MelanieT/PiLomar-pico-controller/tusb_lwip_glue.c

/* 
 * The MIT License (MIT)
 *
 * Based on tinyUSB example that is: Copyright (c) 2020 Peter Lawrence
 * Modified for Pico by Floris Bos
 *
 * influenced by lrndis https://github.com/fetisov/lrndis
 *
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
 */

#include "tusb_lwip_glue.h"

// HIPPY FIX
#include "pico/sync.h"

/* lwip context */
static struct netif netif_data;

/* shared between tud_network_recv_cb() and service_traffic() */
static struct pbuf *received_frame;

/* this is used by this code, ./class/net/net_driver.c, and usb_descriptors.c */
/* ideally speaking, this should be generated from the hardware's unique ID (if available) */
/* it is suggested that the first byte is 0x02 to indicate a link-local address */

/* network parameters of this MCU */
static ip_addr_t ipaddr = IPADDR4_INIT_BYTES(192, 168, 7, 1);
static const ip_addr_t netmask = IPADDR4_INIT_BYTES(255, 255, 255, 0);
static const ip_addr_t gateway = IPADDR4_INIT_BYTES(0, 0, 0, 0);

/* database IP addresses that can be offered to the host; this must be in RAM to store assigned MAC addresses */
static dhcp_entry_t entries[] =
{
    /* mac ip address                          lease time */
    { {0}, IPADDR4_INIT_BYTES(192, 168, 7, 2), 24 * 60 * 60 },
    { {0}, IPADDR4_INIT_BYTES(192, 168, 7, 3), 24 * 60 * 60 },
    { {0}, IPADDR4_INIT_BYTES(192, 168, 7, 4), 24 * 60 * 60 },
};

static const dhcp_config_t dhcp_config =
{
    .router = IPADDR4_INIT_BYTES(0, 0, 0, 0),  /* router address (if any) */
    .port = 67,                                /* listen port */
    .dns = IPADDR4_INIT_BYTES(0, 0, 0, 0),     /* dns server (if any) */
    "",                                        /* dns suffix */
    .num_entry = TU_ARRAY_SIZE(entries),
    entries
};

static err_t linkoutput_fn(struct netif *netif, struct pbuf *p)
{
    (void)netif;
    
    for (;;)
    {
      /* if TinyUSB isn't ready, we must signal back to lwip that there is nothing we can do */
      if (!tud_ready())
        return ERR_USE;
    
      /* if the network driver can accept another packet, we make it happen */
      // HIPPY FIX
      // Provided a size
      if (tud_network_can_xmit(p->tot_len))
      {
        tud_network_xmit(p, 0 /* unused for this example */);
        return ERR_OK;
      }
    
      /* transfer execution to TinyUSB in the hopes that it will finish transmitting the prior packet */
      tud_task();
    }
}

static err_t output_fn(struct netif *netif, struct pbuf *p, const ip_addr_t *addr)
{
    return etharp_output(netif, p, addr);
}

static err_t netif_init_cb(struct netif *netif)
{
    LWIP_ASSERT("netif != NULL", (netif != NULL));
    netif->mtu = CFG_TUD_NET_MTU;
    netif->flags = NETIF_FLAG_BROADCAST | NETIF_FLAG_ETHARP | NETIF_FLAG_LINK_UP | NETIF_FLAG_UP;
    netif->state = NULL;
    netif->name[0] = 'E';
    netif->name[1] = 'X';
    netif->linkoutput = linkoutput_fn;
    netif->output = output_fn;
    return ERR_OK;
}

void init_lwip(void)
{
    struct netif *netif = &netif_data;
    
    /* Initialize lwip */
    lwip_init();
    
    /* the lwip virtual MAC address must be different from the host's; to ensure this, we toggle the LSbit */
    netif->hwaddr_len = sizeof(tud_network_mac_address);
    memcpy(netif->hwaddr, tud_network_mac_address, sizeof(tud_network_mac_address));
    netif->hwaddr[5] ^= 0x01;

    IP4_ADDR(&ipaddr, 192, 168, tud_network_mac_address[5], 1);
    IP4_ADDR(&entries[0].addr, 192, 168, tud_network_mac_address[5], 2);
    IP4_ADDR(&entries[1].addr, 192, 168, tud_network_mac_address[5], 3);
    IP4_ADDR(&entries[2].addr, 192, 168, tud_network_mac_address[5], 4);

    netif = netif_add(netif, &ipaddr, &netmask, &gateway, NULL, netif_init_cb, ip_input);
    netif_set_default(netif);
}

void tud_network_init_cb(void)
{
    /* if the network is re-initializing and we have a leftover packet, we must do a cleanup */
    if (received_frame)
    {
      pbuf_free(received_frame);
      received_frame = NULL;
    }
}

bool tud_network_recv_cb(const uint8_t *src, uint16_t size)
{
    /* this shouldn't happen, but if we get another packet before 
    parsing the previous, we must signal our inability to accept it */
    if (received_frame) return false;
    
    if (size)
    {
        struct pbuf *p = pbuf_alloc(PBUF_RAW, size, PBUF_POOL);

        if (p)
        {
            /* pbuf_alloc() has already initialized struct; all we need to do is copy the data */
            memcpy(p->payload, src, size);
        
            /* store away the pointer for service_traffic() to later handle */
            received_frame = p;
        }
    }

    return true;
}

uint16_t tud_network_xmit_cb(uint8_t *dst, void *ref, uint16_t arg)
{
    struct pbuf *p = (struct pbuf *)ref;
    struct pbuf *q;
    uint16_t len = 0;

    (void)arg; /* unused for this example */

    /* traverse the "pbuf chain"; see ./lwip/src/core/pbuf.c for more info */
    for(q = p; q != NULL; q = q->next)
    {
        memcpy(dst, (char *)q->payload, q->len);
        dst += q->len;
        len += q->len;
        if (q->len == q->tot_len) break;
    }

    return len;
}

void service_traffic(void)
{
    /* handle any packet received by tud_network_recv_cb() */
    if (received_frame)
    {
      ethernet_input(received_frame, &netif_data);
      pbuf_free(received_frame);
      received_frame = NULL;
      tud_network_recv_renew();
    }
    
    sys_check_timeouts();
}

void dhcpd_init()
{
    while (dhserv_init(&dhcp_config) != ERR_OK);    
}

void wait_for_netif_is_up()
{
    while (!netif_is_up(&netif_data));    
}


/* lwip platform specific routines for Pico */
static mutex_t lwip_mutex;
static int lwip_mutex_count = 0;

sys_prot_t sys_arch_protect(void)
{
    uint32_t owner;
    if (!mutex_try_enter(&lwip_mutex, &owner))
    {
        if (owner != get_core_num())
        {
            // Wait until other core releases mutex
            mutex_enter_blocking(&lwip_mutex);
        }
    }

    lwip_mutex_count++;
    
    return 0;
}

void sys_arch_unprotect(sys_prot_t pval)
{
    (void)pval;
    
    if (lwip_mutex_count)
    {
        lwip_mutex_count--;
        if (!lwip_mutex_count)
        {
            mutex_exit(&lwip_mutex);
        }
    }
}

uint32_t sys_now(void)
{
    return to_ms_since_boot( get_absolute_time() );
}
