MelanieT/PiLomar-pico-controller/usb_descriptors-cdc.c

// SPDX-License-Identifier: MIT
/*
 * Copyright (c) 2021 Álvaro Fernández Rojas <noltari@gmail.com>
 *
 * This file is based on a file originally part of the
 * MicroPython project, http://micropython.org/
 *
 * Copyright (c) 2020 Raspberry Pi (Trading) Ltd.
 * Copyright (c) 2019 Damien P. George
 */

#include <hardware/flash.h>
#include <tusb.h>

#define DESC_STR_MAX 20

#define USBD_VID 0x2E8A /* Raspberry Pi */
#define USBD_PID 0x000A /* Raspberry Pi Pico SDK CDC */

#define USBD_DESC_LEN (TUD_CONFIG_DESC_LEN + TUD_CDC_DESC_LEN * CFG_TUD_CDC)
#define USBD_MAX_POWER_MA 500

#define USBD_ITF_CDC_0 0
#if CFG_TUD_CDC == 2
#define USBD_ITF_CDC_1 2
#define USBD_ITF_MAX 4
#else
#define USBD_ITF_MAX 2
#endif

#define USBD_CDC_0_EP_CMD 0x81
#define USBD_CDC_1_EP_CMD 0x83

#define USBD_CDC_0_EP_OUT 0x01
#define USBD_CDC_1_EP_OUT 0x03

#define USBD_CDC_0_EP_IN 0x82
#define USBD_CDC_1_EP_IN 0x84

#define USBD_CDC_CMD_MAX_SIZE 8
#define USBD_CDC_IN_OUT_MAX_SIZE 64

#define USBD_STR_0 0x00
#define USBD_STR_SERIAL_LEN 17

#define EPNUM_NET_NOTIF   0x81
#define EPNUM_NET_OUT     0x02
#define EPNUM_NET_IN      0x82

// String Descriptor Index
enum
{
    STRID_LANGID = 0,
    STRID_MANUFACTURER,
    STRID_PRODUCT,
    STRID_SERIAL,
    STRID_INTERFACE,
    STRID_MAC
};

enum
{
    ITF_NUM_CDC = 0,
    ITF_NUM_CDC_DATA,
    ITF_NUM_TOTAL
};

enum
{
    CONFIG_ID_RNDIS = 0,
    CONFIG_ID_ECM   = 1,
    CONFIG_ID_COUNT
};


static const tusb_desc_device_t usbd_desc_device = {
	.bLength = sizeof(tusb_desc_device_t),
	.bDescriptorType = TUSB_DESC_DEVICE,
	.bcdUSB = 0x0200,
	.bDeviceClass = TUSB_CLASS_MISC,
	.bDeviceSubClass = MISC_SUBCLASS_COMMON,
	.bDeviceProtocol = MISC_PROTOCOL_IAD,
	.bMaxPacketSize0 = CFG_TUD_ENDPOINT0_SIZE,
	.idVendor = USBD_VID,
	.idProduct = USBD_PID,
	.bcdDevice = 0x0100,
	.iManufacturer = STRID_MANUFACTURER,
	.iProduct = STRID_PRODUCT,
	.iSerialNumber = STRID_SERIAL,
	.bNumConfigurations = 2,
};

static const uint8_t usbd_desc_cfg[USBD_DESC_LEN] = {
	TUD_CONFIG_DESCRIPTOR(1, USBD_ITF_MAX, USBD_STR_0, USBD_DESC_LEN,
		TUSB_DESC_CONFIG_ATT_REMOTE_WAKEUP, USBD_MAX_POWER_MA),

	TUD_CDC_DESCRIPTOR(USBD_ITF_CDC_0, STRID_INTERFACE, USBD_CDC_0_EP_CMD,
		USBD_CDC_CMD_MAX_SIZE, USBD_CDC_0_EP_OUT, USBD_CDC_0_EP_IN,
		USBD_CDC_IN_OUT_MAX_SIZE),

#if CFG_TUD_CDC == 2
	TUD_CDC_DESCRIPTOR(USBD_ITF_CDC_1, STRID_INTERFACE, USBD_CDC_1_EP_CMD,
		USBD_CDC_CMD_MAX_SIZE, USBD_CDC_1_EP_OUT, USBD_CDC_1_EP_IN,
		USBD_CDC_IN_OUT_MAX_SIZE),
#endif
};

#define MAIN_CONFIG_TOTAL_LEN    (TUD_CONFIG_DESC_LEN + TUD_RNDIS_DESC_LEN)
#define ALT_CONFIG_TOTAL_LEN     (TUD_CONFIG_DESC_LEN + TUD_CDC_ECM_DESC_LEN)

static uint8_t const rndis_configuration[] =
{
    // Config number (index+1), interface count, string index, total length, attribute, power in mA
    TUD_CONFIG_DESCRIPTOR(CONFIG_ID_RNDIS+1, ITF_NUM_TOTAL, 0, MAIN_CONFIG_TOTAL_LEN, 0, 100),

    // Interface number, string index, EP notification address and size, EP data address (out, in) and size.
    TUD_RNDIS_DESCRIPTOR(ITF_NUM_CDC, STRID_INTERFACE, EPNUM_NET_NOTIF, 8, EPNUM_NET_OUT, EPNUM_NET_IN, CFG_TUD_NET_ENDPOINT_SIZE),
};

static uint8_t const ecm_configuration[] =
{
    // Config number (index+1), interface count, string index, total length, attribute, power in mA
    TUD_CONFIG_DESCRIPTOR(CONFIG_ID_ECM+1, ITF_NUM_TOTAL, 0, ALT_CONFIG_TOTAL_LEN, 0, 100),

    // Interface number, description string index, MAC address string index, EP notification address and size, EP data address (out, in), and size, max segment size.
    TUD_CDC_ECM_DESCRIPTOR(ITF_NUM_CDC, STRID_INTERFACE, STRID_MAC, EPNUM_NET_NOTIF, 64, EPNUM_NET_OUT, EPNUM_NET_IN, CFG_TUD_NET_ENDPOINT_SIZE, CFG_TUD_NET_MTU),
};

static char usbd_serial[USBD_STR_SERIAL_LEN] = "000000000000";

#define _PID_MAP(itf, n)  ( (CFG_TUD_##itf) << (n) )
#define USB_PID           (0x4000 | _PID_MAP(CDC, 0) | _PID_MAP(MSC, 1) | _PID_MAP(HID, 2) | \
                           _PID_MAP(MIDI, 3) | _PID_MAP(VENDOR, 4) | _PID_MAP(ECM_RNDIS, 5) | _PID_MAP(NCM, 5) )

static const char *const usbd_desc_str[] = {
	[STRID_MANUFACTURER] = "Raspberry Pi",
	[STRID_PRODUCT] = "Pico",
	[STRID_SERIAL] = usbd_serial,
	[STRID_INTERFACE] = "Pilomar",
};

const uint8_t *tud_descriptor_device_cb(void)
{
	return (const uint8_t *) &usbd_desc_device;
}

const uint8_t *tud_descriptor_configuration_cb(uint8_t index)
{
	return usbd_desc_cfg;
}

const uint16_t *tud_descriptor_string_cb(uint8_t index, uint16_t langid)
{
    static uint16_t desc_str[DESC_STR_MAX];
    uint8_t len = 0;

    if (index == STRID_LANGID) {
        desc_str[1] = 0x0409;
        len = 1;
    }
    else if(index == STRID_MAC) {
        // Convert MAC address into UTF-16
        for (unsigned i=0; i<sizeof(tud_network_mac_address); i++) {
            desc_str[1+len++] = "0123456789ABCDEF"[(tud_network_mac_address[i] >> 4) & 0xf];
            desc_str[1+len++] = "0123456789ABCDEF"[(tud_network_mac_address[i] >> 0) & 0xf];
        }
    }
    else
    {
        const char *str;

        if (index >= sizeof(usbd_desc_str) / sizeof(usbd_desc_str[0]))
            return NULL;

        str = usbd_desc_str[index];
        for (len = 0; len < DESC_STR_MAX - 1 && str[len]; ++len)
            desc_str[1 + len] = str[len];
    }

    desc_str[0] = (TUSB_DESC_STRING << 8) | (2 * len + 2);

	return desc_str;
}

uint8_t tud_network_mac_address[6];

void usbd_serial_init(void)
{
	uint8_t id[8];

	flash_get_unique_id(id);

	snprintf(usbd_serial, USBD_STR_SERIAL_LEN, "%02X%02X%02X%02X%02X%02X%02X%02X",
		 id[0], id[1], id[2], id[3], id[4], id[5], id[6], id[7]);

    tud_network_mac_address[0] = id[2];
    tud_network_mac_address[1] = id[3];
    tud_network_mac_address[2] = id[4];
    tud_network_mac_address[3] = id[5];
    tud_network_mac_address[4] = id[6];
    tud_network_mac_address[5] = id[7];
}
