MelanieT/PiLomar-pico-controller/lwipopts.h

// SPDX-FileCopyrightText: 2024 Melanie Thielker & Leonie Gaertner
// SPDX-License-Identifier: BSD-3-Clause

#ifndef __LWIPOPTS_H__
#define __LWIPOPTS_H__

/* Prevent having to link sys_arch.c (we don't test the API layers in unit tests) */
#define NO_SYS                          1
#define MEM_ALIGNMENT                   4
#define LWIP_RAW                        1
#define MEM_SIZE                        4000
#define MEMP_NUM_TCP_SEG                32
#define MEMP_NUM_ARP_QUEUE              10
#define PBUF_POOL_SIZE                  24
#define LWIP_ARP                        1
#define LWIP_ETHERNET                   1
#define LWIP_NETCONN                    0
#define LWIP_SOCKET                     0
#define LWIP_DHCP                       0
#define LWIP_ICMP                       1
#define LWIP_UDP                        1
#define LWIP_TCP                        1
#define ETH_PAD_SIZE                    0
#define LWIP_IP_ACCEPT_UDP_PORT(p)      ((p) == PP_NTOHS(67))
#define LWIP_TCP_KEEPALIVE          1
#define LWIP_NETIF_TX_SINGLE_PBUF   1

#define TCP_MSS                         (1500 /*mtu*/ - 20 /*iphdr*/ - 20 /*tcphhr*/)
#define TCP_SND_BUF                     (2 * TCP_MSS)

#define ETHARP_SUPPORT_STATIC_ENTRIES   1

#define LWIP_HTTPD_CGI                  0
#define LWIP_HTTPD_SSI                  0
#define LWIP_HTTPD_SSI_INCLUDE_TAG      0
#define HTTPD_USE_CUSTOM_FSDATA         0
// #define HTTPD_FSDATA_FILE               "../../../../fsdata.c"
// #define HTTPD_FSDATA_FILE               "fsdata.c"

#define LWIP_SINGLE_NETIF               1

#endif /* __LWIPOPTS_H__ */
