MelanieT/PiLomar-pico-controller/webserver/UrlMapper.cpp

// SPDX-FileCopyrightText: 2024 Melanie Thielker & Leonie Gaertner
// SPDX-License-Identifier: BSD-3-Clause

#include "UrlMapper.h"
#include "HttpStatus.h"

#include <utility>

Url::Url(std::string method, std::string url, void (*handler)(const HttpRequest& request, HttpResponse& response))
{
    m_method = std::move(method);
    m_url = std::move(url);
    m_handler = handler;
}

std::string Url::method()
{
    return m_method;
}

std::string Url::url()
{
    return m_url;
}

void Url::call(const HttpRequest &request, HttpResponse &response)
{
    (*m_handler)(request, response);
}

UrlMapper::UrlMapper()
= default;

std::list<Url> UrlMapper::m_mapping;

void UrlMapper::AddMapping(std::string method, std::string url, void (*handler)(const HttpRequest &, HttpResponse &))
{
    auto map = Url(std::move(method), std::move(url), handler);
    m_mapping.emplace_back(map);
}

void UrlMapper::Map(const HttpRequest& request, HttpResponse& response)
{
    for (Url mapping : m_mapping)
    {
        if (request.method() == mapping.method() && request.url() == mapping.url())
        {
            mapping.call(request, response);
            return;
        }
    }
    response.setStatusCode(HttpStatus::Code::NotFound);
}
